Ottercast/OtterCastAudioV2/CAD/g1002.png

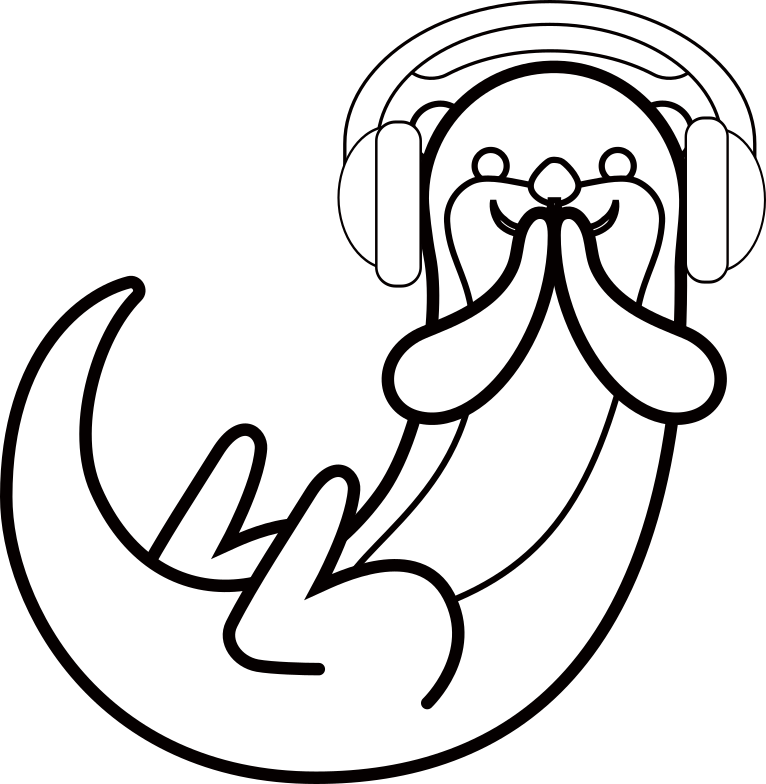
CAD/g1002.png
