Ottercast/OtterCastAudioV2/graphics/amp_out.png

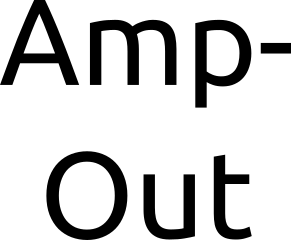
graphics/amp_out.png
