Ottercast/OtterCastAudioV2/graphics/by.png

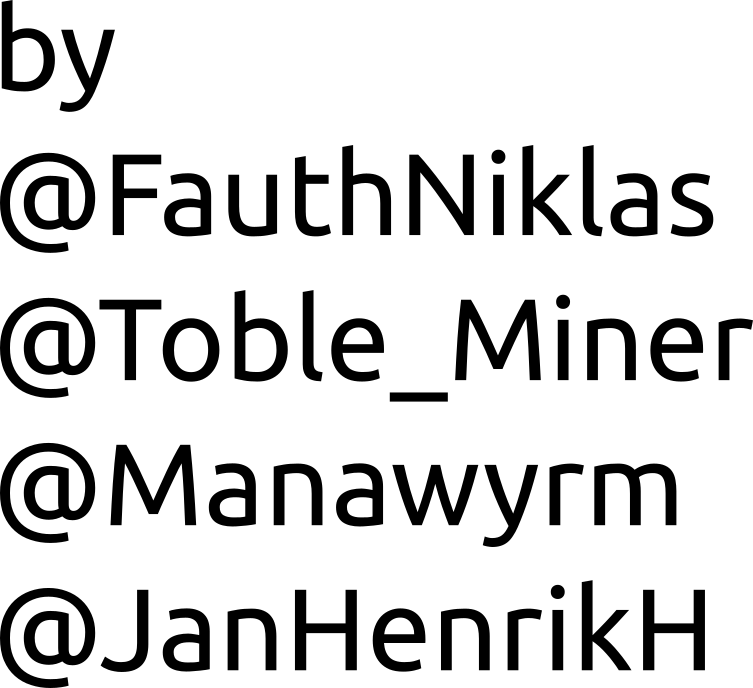
graphics/by.png
