Ottercast/OtterCastAudioV2/graphics/hw_v2.1.png

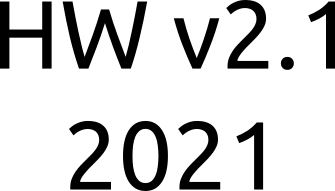
graphics/hw_v2.1.png
