Ottercast/OtterCastAudioV2/graphics/line_in.png

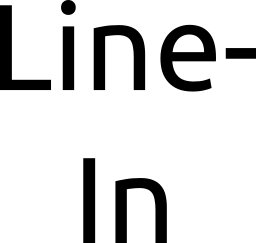
graphics/line_in.png
