Ottercast/OtterCastAudioV2/graphics/line_out.png

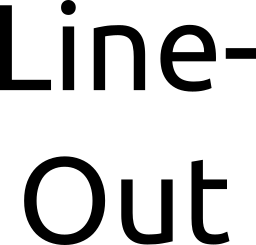
graphics/line_out.png
