Ottercast/OtterCastAudioV2/graphics/OtterCastAudioV2.png

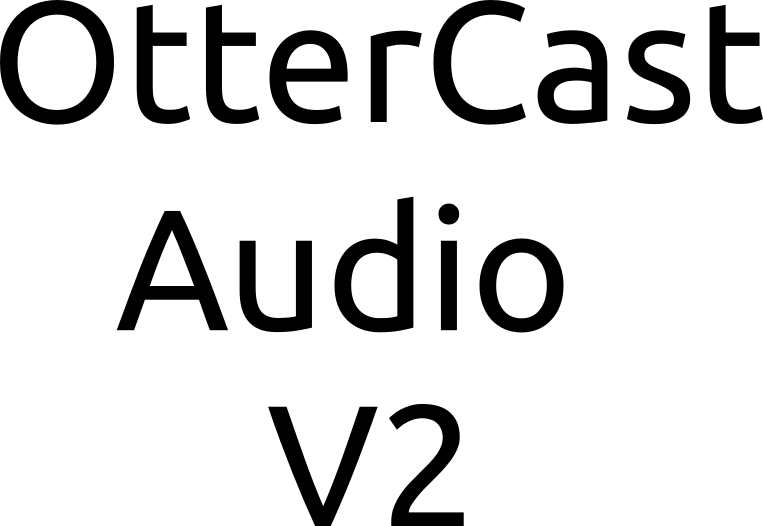
graphics/OtterCastAudioV2.png
