Ottercast/OtterCastAudioV2/graphics/OtterCastAudioV2_3.png

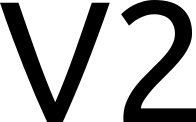
graphics/OtterCastAudioV2_3.png
