Ottercast/OtterCastAudioV2/graphics/OtterCastAudioV21_3.png

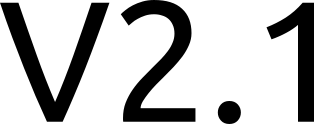
graphics/OtterCastAudioV21_3.png
