Ottercast/OtterCastAudioV2/production_v2.1/OtteCastv21_Combined_Top.png

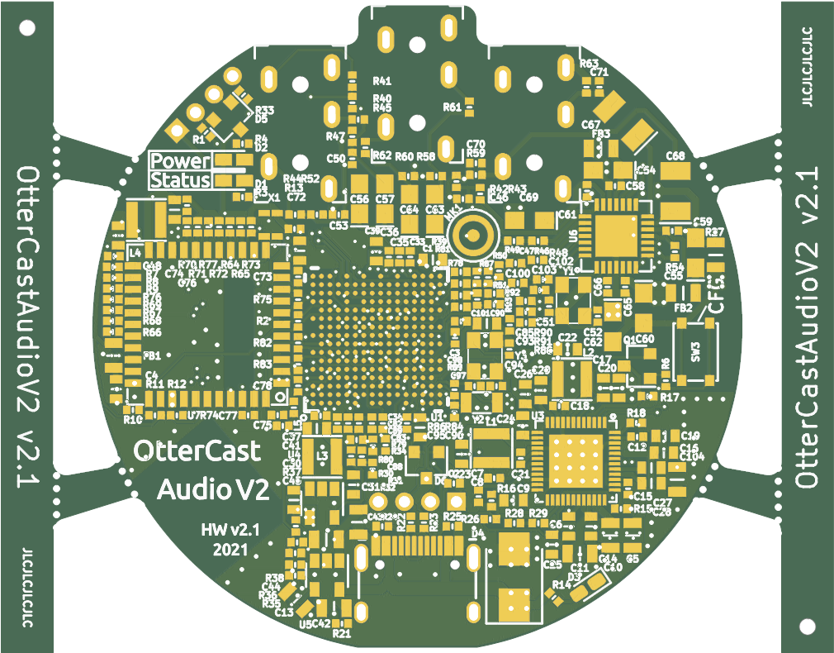
production_v2.1/OtteCastv21_Combined_Top.png
